KimIV/LatencyMeter/3D_Model_OutSensors/Holder-Lens.png

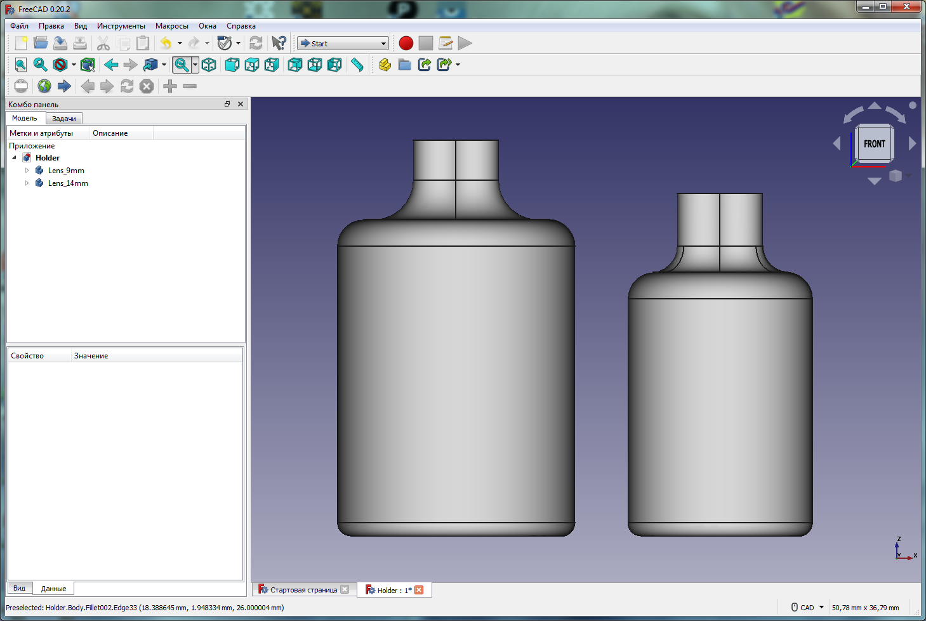
3D_Model_OutSensors/Holder-Lens.png
