KimIV/LatencyMeter/3D_Model_OutSensors/Holder-Lens_9mm_Sketch.png

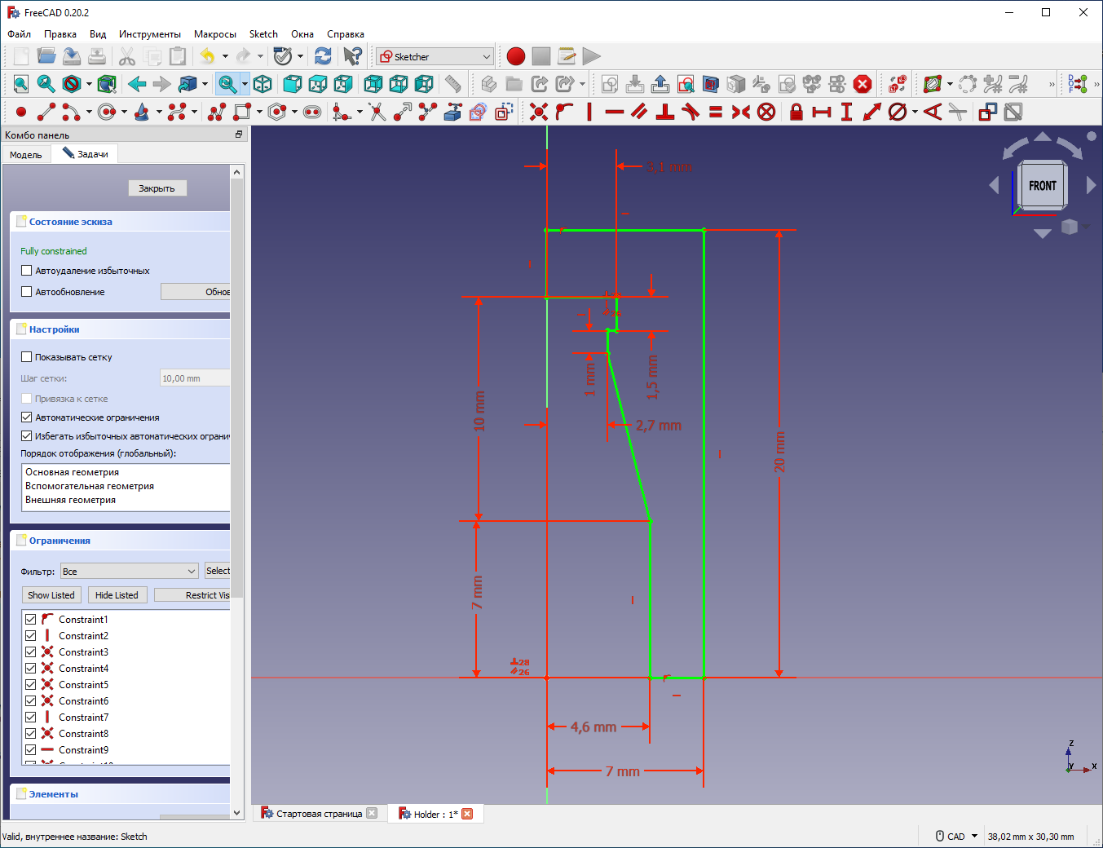
3D_Model_OutSensors/Holder-Lens_9mm_Sketch.png
