KimIV/LatencyMeter/3D_Model_OutSensors/Holder-Lens_14mm_1.png

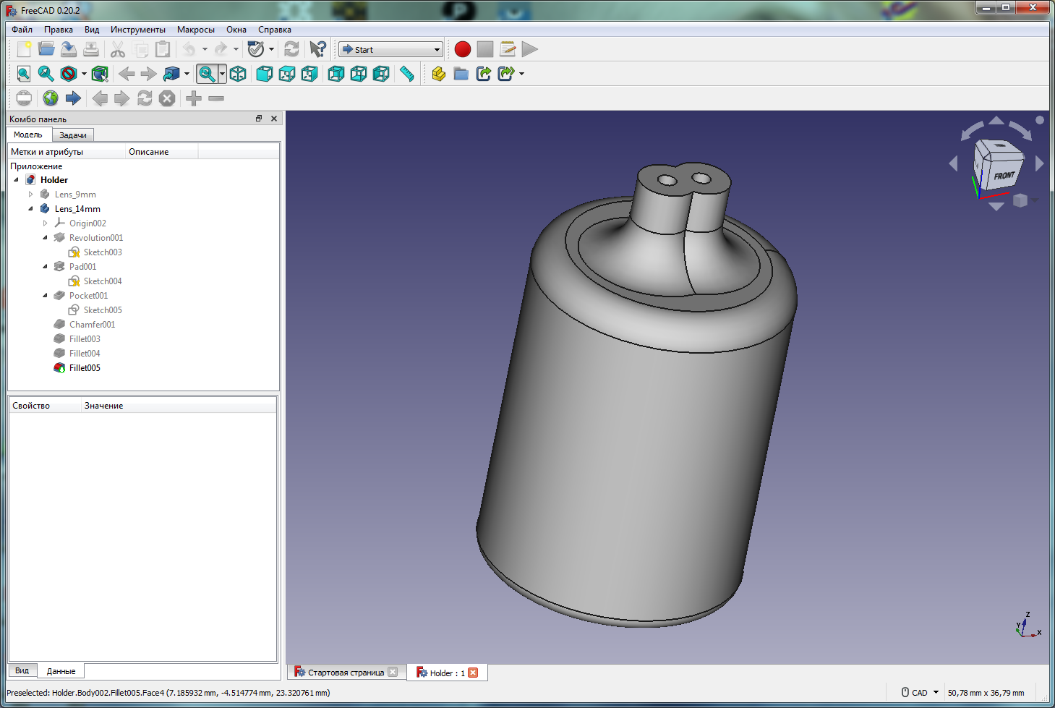
3D_Model_OutSensors/Holder-Lens_14mm_1.png
