KimIV/LatencyMeter/3D_Model_OutSensors/Holder-Lens_14mm_2.png

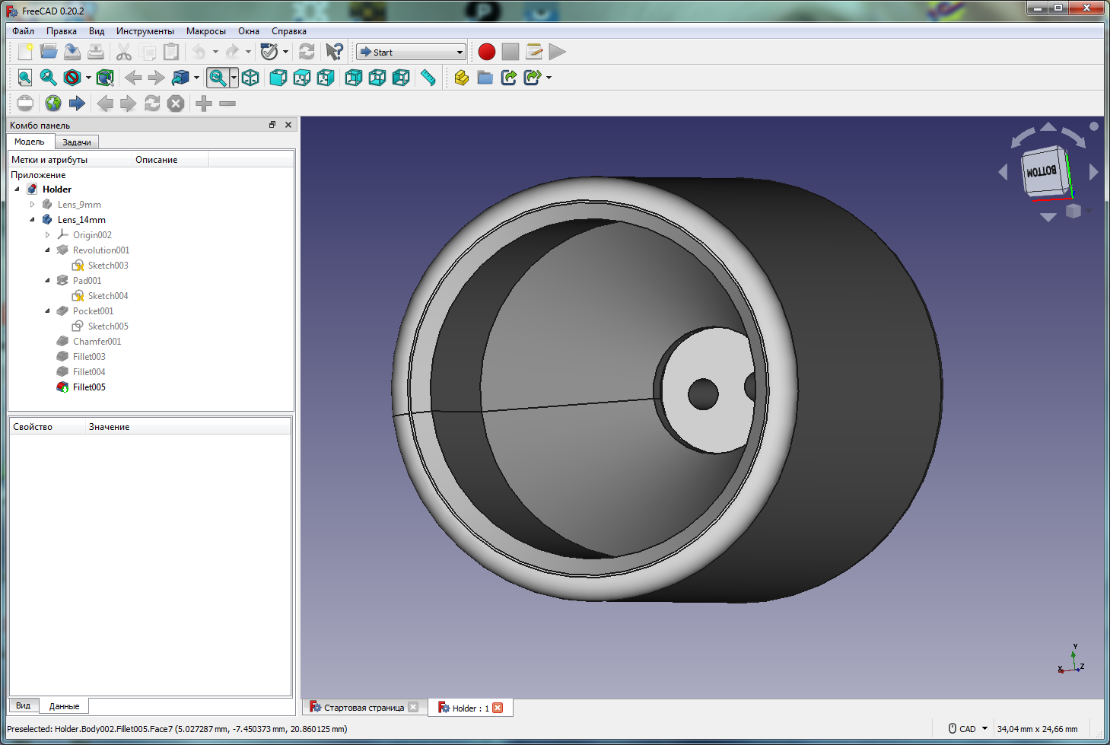
3D_Model_OutSensors/Holder-Lens_14mm_2.png
