KimIV/LatencyMeter/3D_Model_OutSensors/Holder-PhotoResistor.png

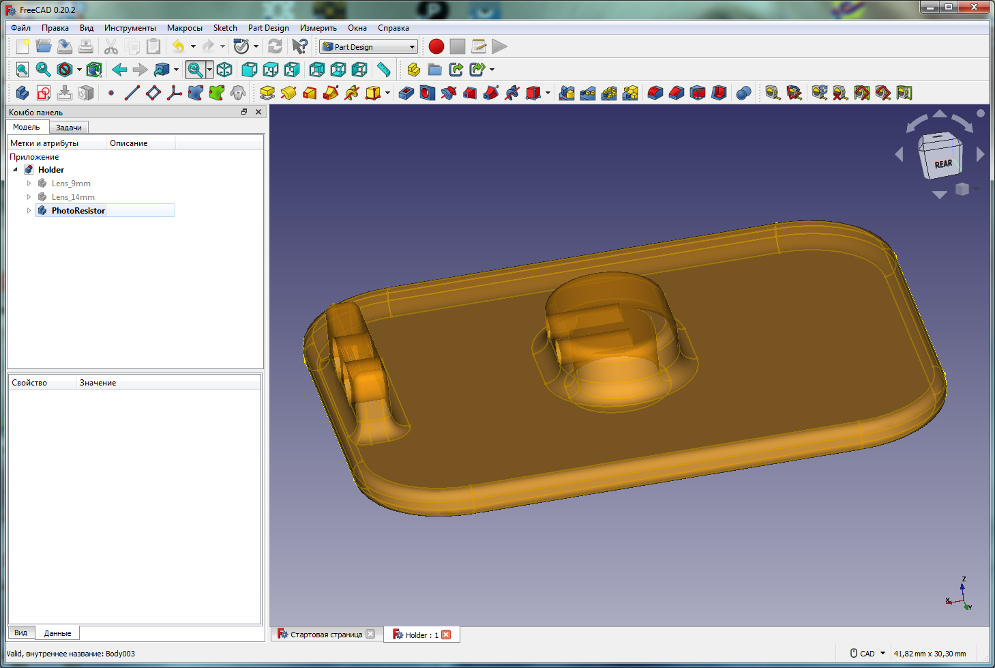
3D_Model_OutSensors/Holder-PhotoResistor.png
