KimIV/LatencyMeter/3D_Model_OutSensors/Holder-PhotoResistor_2.png

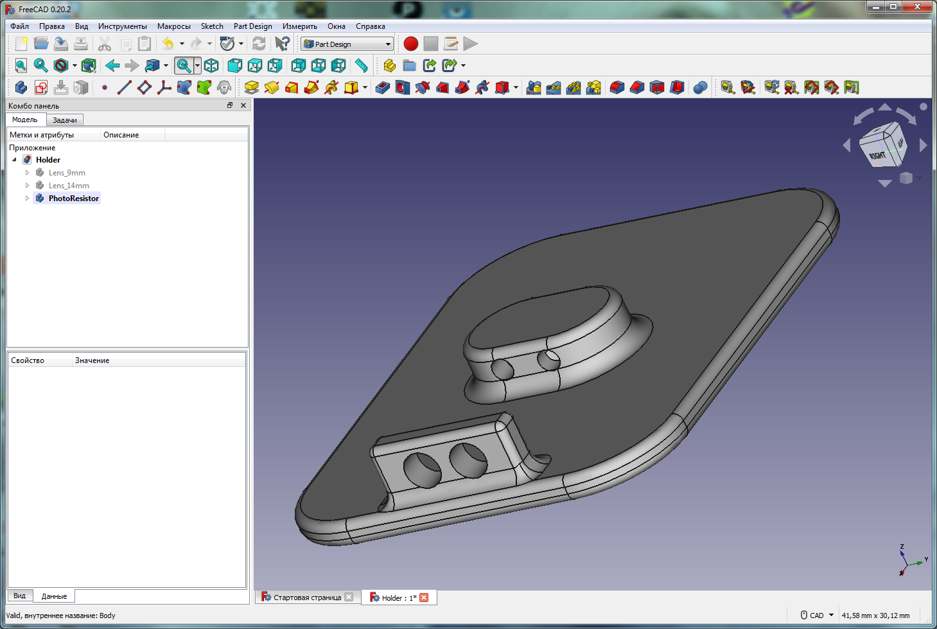
3D_Model_OutSensors/Holder-PhotoResistor_2.png
