KimIV/LatencyMeter/3D_Model_OutSensors/Image 4.png

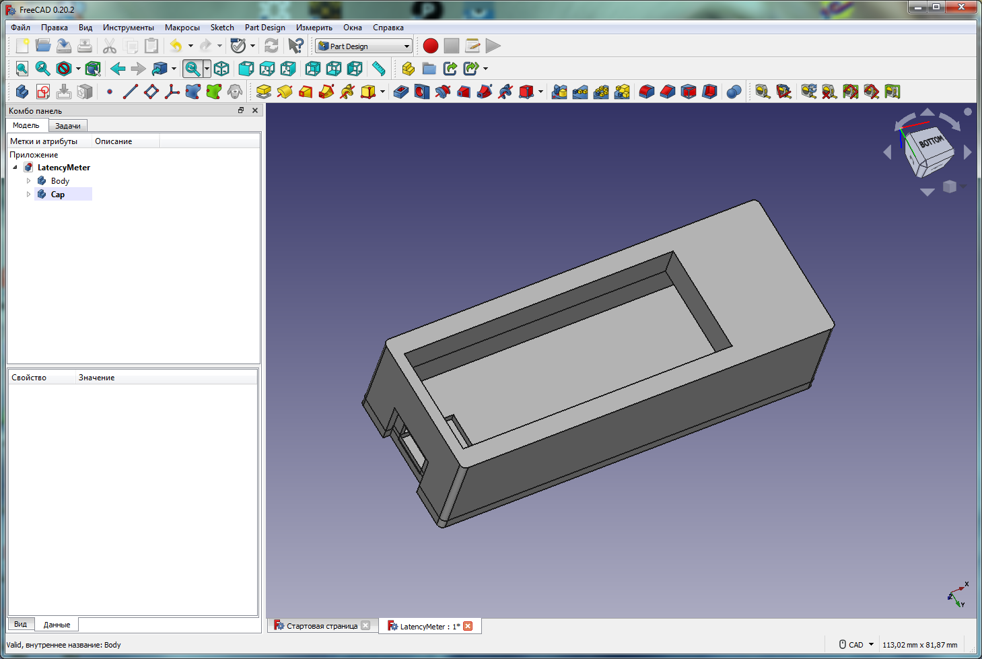
3D_Model_OutSensors/Image 4.png
