KimIV/LatencyMeter/3D_Model_OutSensors/Image 5.png

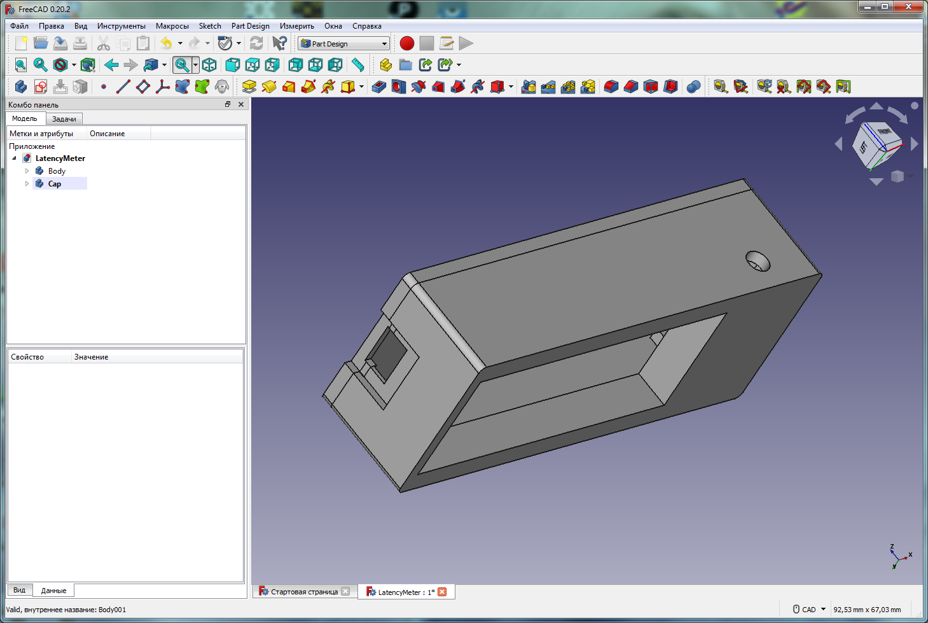
3D_Model_OutSensors/Image 5.png
