KimIV/LatencyMeter/3D_Model_OutSensors/Image 6.png

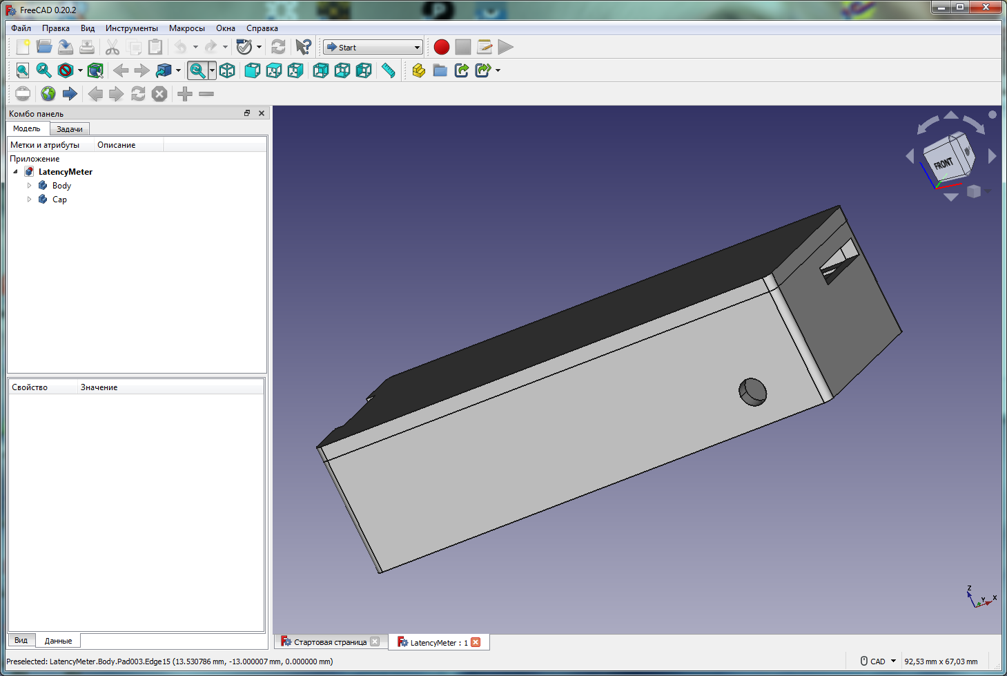
3D_Model_OutSensors/Image 6.png
