KimIV/LatencyMeter/3D_Model_OutSensors/Image 7.png

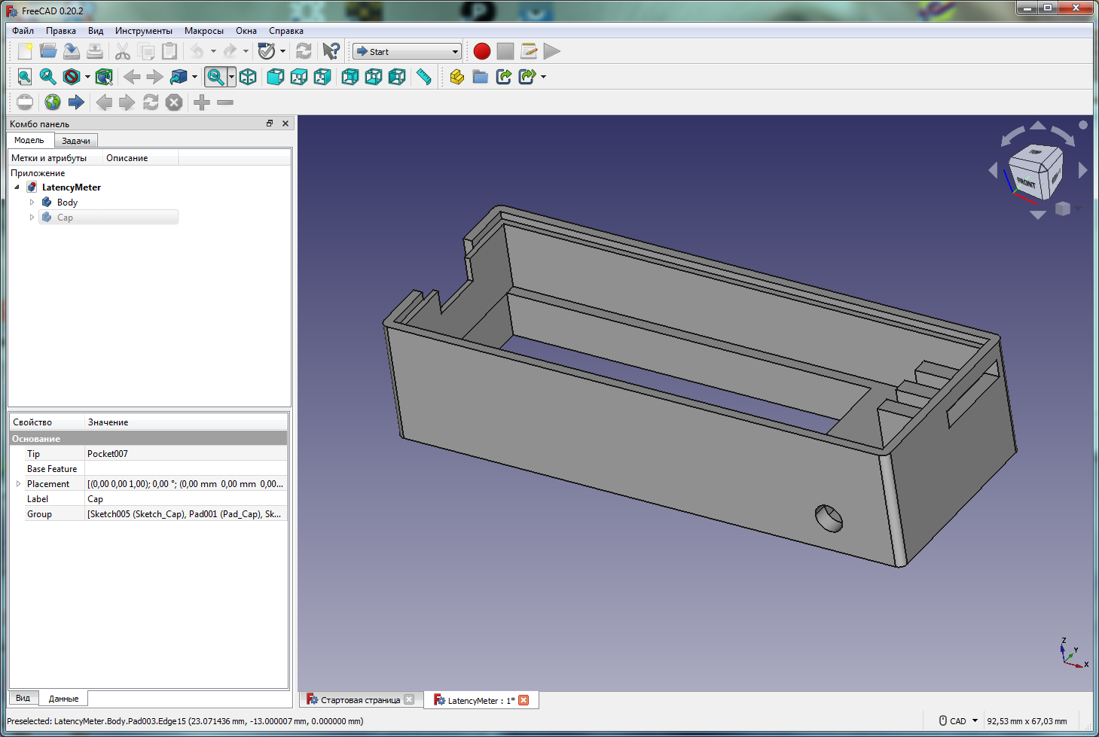
3D_Model_OutSensors/Image 7.png
